nksb92/rlcv3/3d_models/Tube/Stand/floor_stand.FCStd

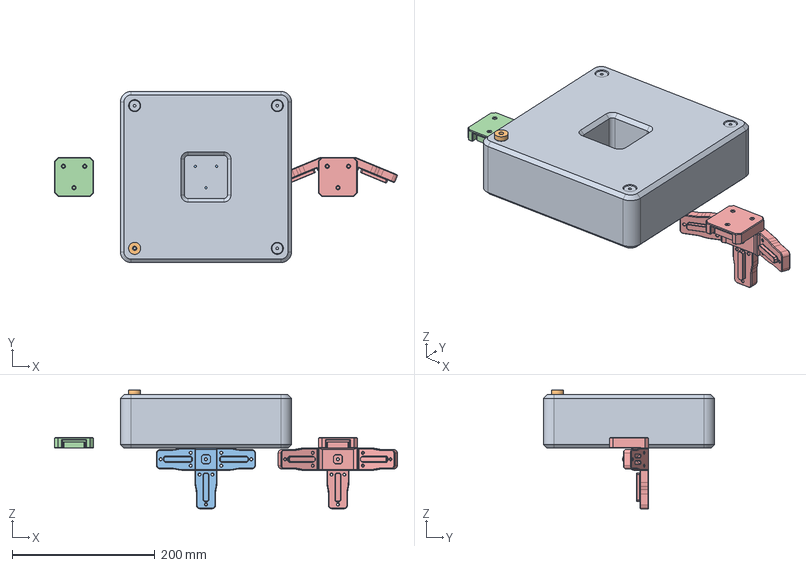
[picture p16: CAD file, 2026-02-27]
3d_models/Tube/Stand/floor_stand.FCStd
480.9 x 240.0 x 166.3 mm
hollow
feet
interface_tube_t_section_clamp
interface_tube_base_clamp
interface_tube_t_section_45°
