nksb92/rlcv3/3d_models/Tube/Connectors/rlcv3_connector_clamp_3.3mf

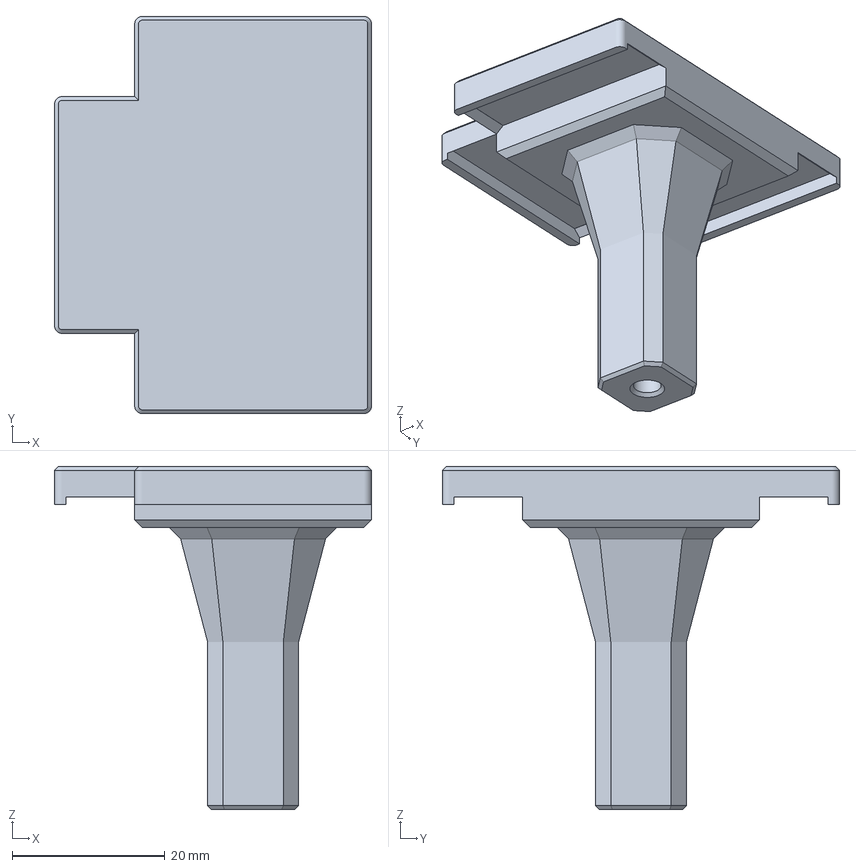
[picture p17: CAD file, 2026-02-27]
3d_models/Tube/Connectors/rlcv3_connector_clamp_3.3mf
41.5 x 52.0 x 44.9 mm
