nksb92/rlcv3/3d_models/Tube/Enclosure/display_spacer.FCStd

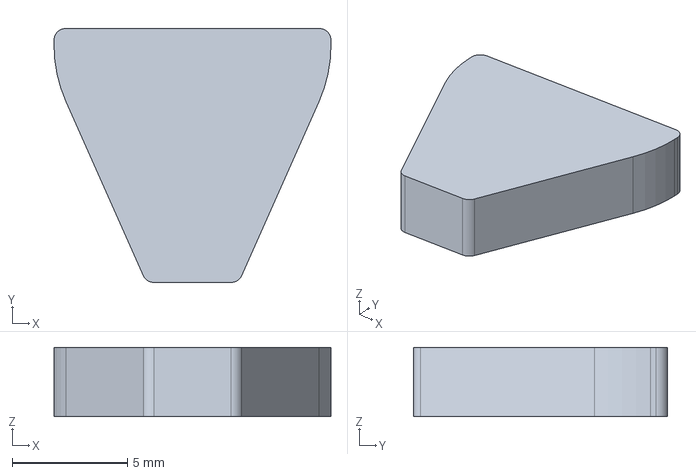
[picture p18: CAD file, 2026-02-27]
3d_models/Tube/Enclosure/display_spacer.FCStd
12.0 x 11.0 x 3.00 mm
