nksb92/rlcv3/3d_models/Tube/Stand/floor_stand_funnel_holder.3mf

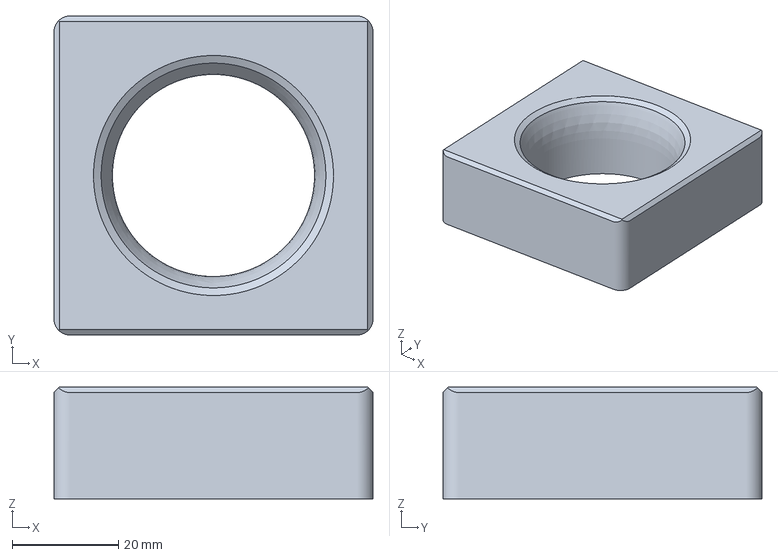
[picture p19: CAD file, 2026-02-27]
3d_models/Tube/Stand/floor_stand_funnel_holder.3mf
60.0 x 60.0 x 21.0 mm
