nksb92/rlcv3/3d_models/Tube/Connectors/rlcv3_connector_90_degree.3mf

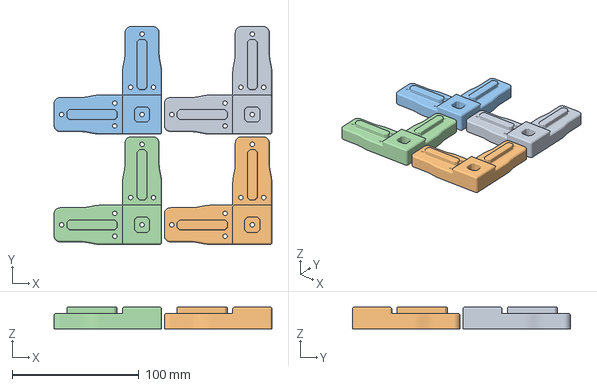
[picture p20: CAD file, 2026-02-27]
3d_models/Tube/Connectors/rlcv3_connector_90_degree.3mf
172.0 x 172.0 x 17.0 mm
