nksb92/rlcv3/3d_models/Tube/Enclosure/rlcv3_bottom.stp

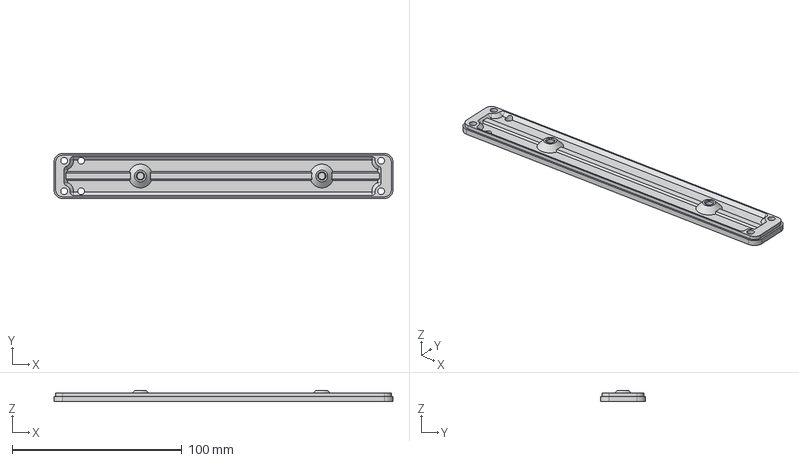
[picture p21: CAD file, 2026-02-27]
3d_models/Tube/Enclosure/rlcv3_bottom.stp
200.0 x 26.5 x 6.50 mm
