nksb92/rlcv3/3d_models/Tube/Stand/floor_stand_funnel.3mf

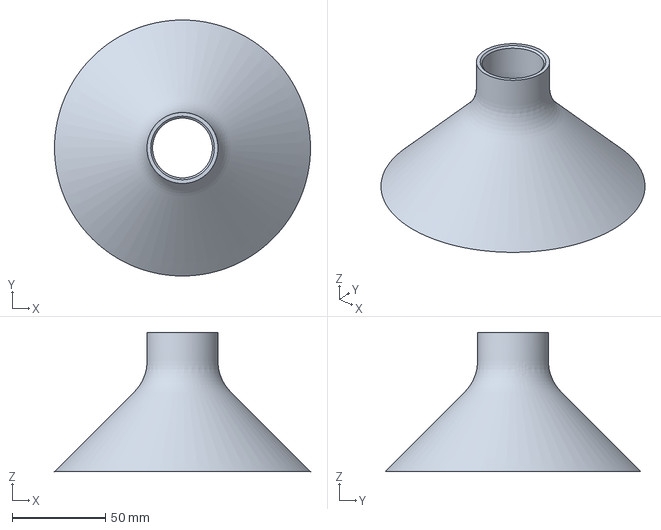
[picture p22: CAD file, 2026-02-27]
3d_models/Tube/Stand/floor_stand_funnel.3mf
137.0 x 137.0 x 74.5 mm
