nksb92/rlcv3/3d_models/Tube/Connectors/rlcv3_connector_t_section_45°.3mf

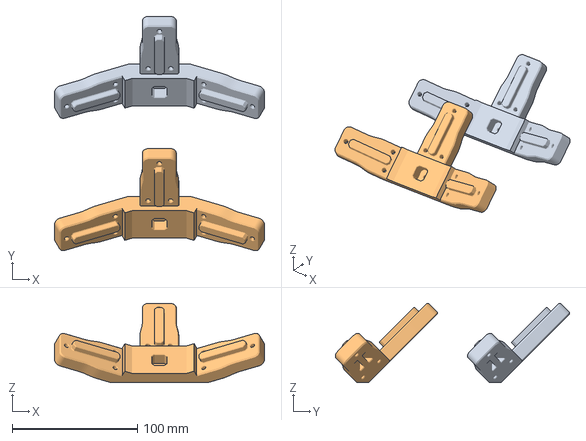
[picture p23: CAD file, 2026-02-27]
3d_models/Tube/Connectors/rlcv3_connector_t_section_45°.3mf
167.4 x 186.8 x 63.2 mm
