nksb92/rlcv3/3d_models/Tube/Enclosure/rlcv3_top.stp

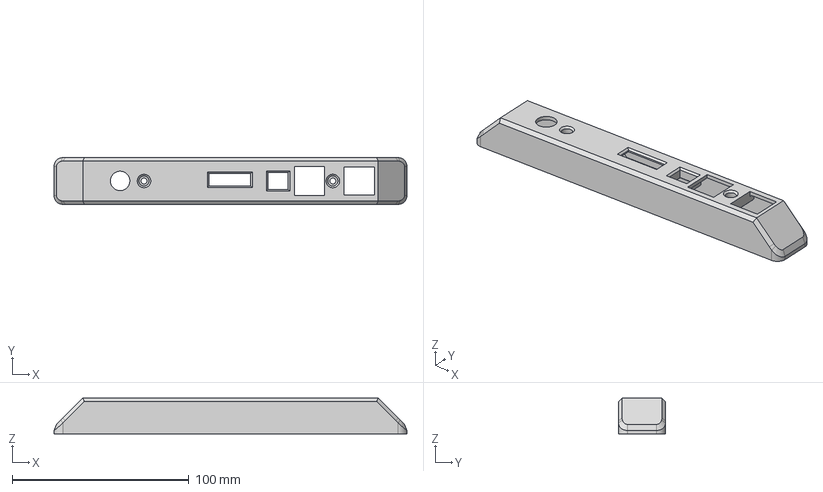
[picture p24: CAD file, 2026-02-27]
3d_models/Tube/Enclosure/rlcv3_top.stp
200.0 x 26.5 x 20.4 mm
