nksb92/rlcv3/3d_models/Tube/Connectors/rlcv3_connector_t_section.3mf

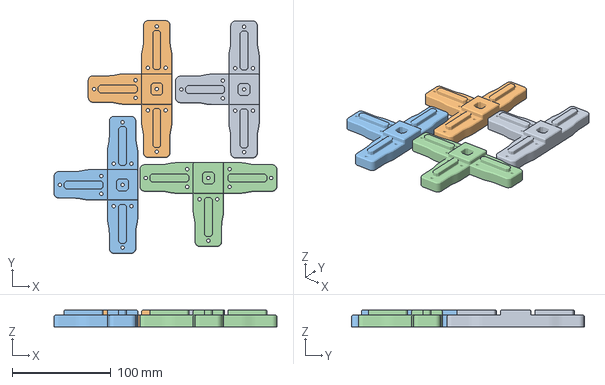
[picture p25: CAD file, 2026-02-27]
3d_models/Tube/Connectors/rlcv3_connector_t_section.3mf
226.0 x 236.1 x 17.0 mm
