nksb92/rlcv3/3d_models/Tube/Connectors/rlcv3_connector_adapter_spots_connector.3mf

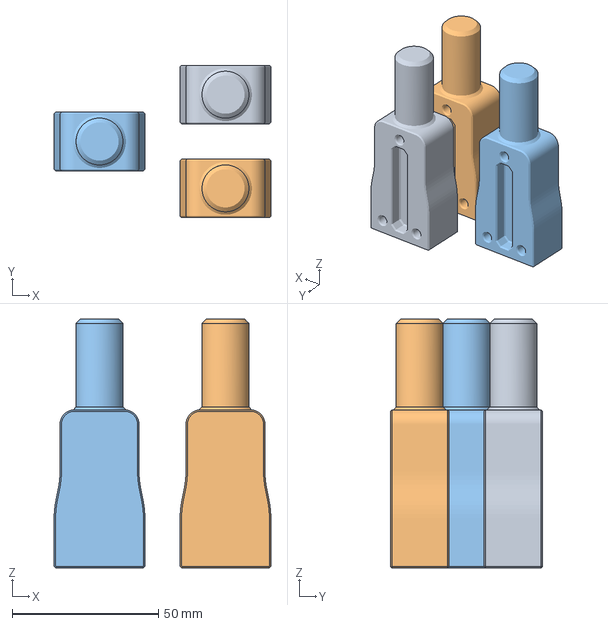
[picture p26: CAD file, 2026-02-27]
3d_models/Tube/Connectors/rlcv3_connector_adapter_spots_connector.3mf
74.0 x 52.0 x 85.0 mm
