nksb92/rlcv3/RLC_V3/nvm.cpp

#include "nvm.h"

#define COUNT_STORED_VALUES 14
#define POLYNOMIAL 0xD8
#define WIDTH (8 * sizeof(uint8_t))
#define TOPBIT (1 << (WIDTH - 1))
#define REFLECT_DATA(X) ((uint8_t)reflect((X), 8))
#define REFLECT_REMAINDER(X) ((uint8_t)reflect((X), WIDTH))
uint8_t crcTable[256];

// crc code from website: https://barrgroup.com/embedded-systems/how-to/crc-calculation-c-code
// explaination can be found there
void crcInit() {
  uint8_t remainder;

  for (int dividend = 0; dividend < 256; ++dividend) {
    remainder = dividend << (WIDTH - 8);

    for (uint8_t bit = 8; bit > 0; --bit) {
      if (remainder & TOPBIT) {
        remainder = (remainder << 1) ^ POLYNOMIAL;
      } else {
        remainder = (remainder << 1);
      }
    }
    crcTable[dividend] = remainder;
  }
}

uint8_t crcFast(int message[]) {
  uint8_t data;
  uint8_t remainder = 0;
  int nBytes = sizeof(message);

  for (int byte = 0; byte < nBytes; ++byte) {
    data = message[byte] ^ (remainder >> (WIDTH - 8));
    remainder = crcTable[data] ^ (remainder << 8);
  }

  return (remainder);
}

void init_eeprom() {
  EEPROM.begin(EEPROM_ADDRESSES);
  crcInit();
}

void read_eeprom(C_HSV& hsv_val, C_RGB& rgb_val, rgb_dmx& dmx_val, menu_structure& main_sw, rlc_artnet& artnet_var, segments& segment_var) {
  uint16_t eeprom_address = 0;
  int crc_values[COUNT_STORED_VALUES] = {};
  uint8_t crc_index = 0;

  // get all variables from the hsv page
  uint8_t hue = STD_HUE;
  EEPROM.get(eeprom_address, hue);
  eeprom_address += sizeof(hue);
  crc_values[crc_index] = hue;
  crc_index++;

  uint8_t sat = STD_SAT;
  EEPROM.get(eeprom_address, sat);
  eeprom_address += sizeof(sat);
  crc_values[crc_index] = sat;
  crc_index++;

  uint8_t val = STD_VAL;
  EEPROM.get(eeprom_address, val);
  eeprom_address += sizeof(sat);
  crc_values[crc_index] = val;
  crc_index++;

  // get all variables from the rgb page
  uint8_t red = STD_RED;
  EEPROM.get(eeprom_address, red);
  eeprom_address += sizeof(red);
  crc_values[crc_index] = red;
  crc_index++;

  uint8_t green = STD_GREEN;
  EEPROM.get(eeprom_address, green);
  eeprom_address += sizeof(green);
  crc_values[crc_index] = green;
  crc_index++;

  uint8_t blue = STD_BLUE;
  EEPROM.get(eeprom_address, blue);
  eeprom_address += sizeof(blue);
  crc_values[crc_index] = blue;
  crc_index++;

  // get all variables from the segment page
  uint8_t segment_pos = STD_SEGMENTS;
  EEPROM.get(eeprom_address, segment_pos);
  eeprom_address += sizeof(segment_pos);
  crc_values[crc_index] = segment_pos;
  crc_index++;

  // get all variables from the dmx page
  uint16_t start_address = STD_START_ADDRESS;
  EEPROM.get(eeprom_address, start_address);
  eeprom_address += sizeof(start_address);
  crc_values[crc_index] = start_address;
  crc_index++;

  // get the current main state
  uint8_t current_main = STD_CURRENT;
  EEPROM.get(eeprom_address, current_main);
  eeprom_address += sizeof(current_main);
  crc_values[crc_index] = current_main;
  crc_index++;

  uint8_t deepness_main = STD_DEEPNESS;
  EEPROM.get(eeprom_address, deepness_main);
  eeprom_address += sizeof(deepness_main);
  crc_values[crc_index] = deepness_main;
  crc_index++;

  // get all variables from the artnet page
  uint16_t artnet_universe = STD_UNIVERSE;
  EEPROM.get(eeprom_address, artnet_universe);
  eeprom_address += sizeof(artnet_universe);
  crc_values[crc_index] = artnet_universe;
  crc_index++;

  uint16_t artnet_start = STD_START_ADDRESS;
  EEPROM.get(eeprom_address, artnet_start);
  eeprom_address += sizeof(artnet_start);
  crc_values[crc_index] = artnet_start;
  crc_index++;

  uint8_t artnet_fsm = MENU;
  EEPROM.get(eeprom_address, artnet_fsm);
  eeprom_address += sizeof(artnet_fsm);
  crc_values[crc_index] = artnet_fsm;

  uint8_t crc = 0;
  EEPROM.get(eeprom_address, crc);

  // checking if the saved crc matches the calculated
  // and sets the corresponding variables on success
  if (crc == crcFast(crc_values)) {
    hsv_val.set_hue_byte(hue);
    hsv_val.set_sat(sat);
    hsv_val.set_val(val);

    rgb_val.set_red(red);
    rgb_val.set_green(green);
    rgb_val.set_blue(blue);

    segment_var.set_current_segment(segment_pos);

    dmx_val.set_number_segments(segment_var.get_num_seg());
    artnet_var.set_number_segments(segment_var.get_num_seg());

    dmx_val.set_start_address(start_address);

    main_sw.set_current(current_main);
    main_sw.set_deepness(deepness_main);

    artnet_var.set_current_universe_nmbr(artnet_universe);
    artnet_var.set_current_channel(artnet_start);
    artnet_var.set_current_fsm(artnet_fsm);
  }
}

void write_eeprom(C_HSV& hsv_val, C_RGB& rgb_val, rgb_dmx& dmx_val, menu_structure& main_sw, rlc_artnet& artnet_var, segments& segment_var) {
  uint16_t eeprom_address = 0;
  int crc_values[COUNT_STORED_VALUES] = {};
  uint8_t crc_index = 0;

  // set all variables from the hsv page
  uint8_t hue = hsv_val.get_hue();
  EEPROM.put(eeprom_address, hue);
  eeprom_address += sizeof(hue);
  crc_values[crc_index] = hue;
  crc_index++;

  uint8_t sat = hsv_val.get_sat();
  EEPROM.put(eeprom_address, sat);
  eeprom_address += sizeof(sat);
  crc_values[crc_index] = sat;
  crc_index++;

  uint8_t val = hsv_val.get_val();
  EEPROM.put(eeprom_address, val);
  eeprom_address += sizeof(val);
  crc_values[crc_index] = val;
  crc_index++;

  // set all variables from the rgb page
  uint8_t red = rgb_val.get_red();
  EEPROM.put(eeprom_address, red);
  eeprom_address += sizeof(red);
  crc_values[crc_index] = red;
  crc_index++;

  uint8_t green = rgb_val.get_green();
  EEPROM.put(eeprom_address, green);
  eeprom_address += sizeof(green);
  crc_values[crc_index] = green;
  crc_index++;

  uint8_t blue = rgb_val.get_blue();
  EEPROM.put(eeprom_address, blue);
  eeprom_address += sizeof(blue);
  crc_values[crc_index] = blue;
  crc_index++;

  // set all variables from the segment page
  uint8_t segment_pos = segment_var.get_current_seg();
  EEPROM.put(eeprom_address, segment_pos);
  eeprom_address += sizeof(segment_pos);
  crc_values[crc_index] = segment_pos;
  crc_index++;

  // set all variables from the dmx page
  uint16_t start_address = dmx_val.get_start();
  EEPROM.put(eeprom_address, start_address);
  eeprom_address += sizeof(start_address);
  crc_values[crc_index] = start_address;
  crc_index++;

  // set the all variables from main state
  uint8_t current_main = main_sw.get_current();
  EEPROM.put(eeprom_address, current_main);
  eeprom_address += sizeof(current_main);
  crc_values[crc_index] = current_main;
  crc_index++;

  uint8_t deepness_main = main_sw.get_deepness();
  EEPROM.put(eeprom_address, deepness_main);
  eeprom_address += sizeof(deepness_main);
  crc_values[crc_index] = deepness_main;
  crc_index++;

  // set all variables from the artnet page
  uint16_t artnet_universe = artnet_var.get_start_universe();
  EEPROM.put(eeprom_address, artnet_universe);
  eeprom_address += sizeof(artnet_universe);
  crc_values[crc_index] = artnet_universe;
  crc_index++;

  uint16_t artnet_start = artnet_var.get_start_channel();
  EEPROM.put(eeprom_address, artnet_start);
  eeprom_address += sizeof(artnet_start);
  crc_values[crc_index] = artnet_start;
  crc_index++;

  uint8_t artnet_fsm = artnet_var.get_current_fsm();
  EEPROM.put(eeprom_address, artnet_fsm);
  eeprom_address += sizeof(artnet_fsm);
  crc_values[crc_index] = artnet_fsm;

  // calculate the crc and saving it in the eeprom
  EEPROM.put(eeprom_address, crcFast(crc_values));

  EEPROM.commit();
}
