nksb92/rlcv3/RLC_V3/common.h

#ifndef COMMON_H
#define COMMON_H

#include <Arduino.h>
#include <FastLED.h>

#include "c_hsv.h"
#include "c_rgb.h"
#include "config.h"
#include "menu_structure.h"
#include "rlc_artnet.h"
#include "settings_menu.h"
#include "std_defines.h"

#endif
