nksb92/rlcv3/RLC_V3/src/common.h

#ifndef COMMON_H
#define COMMON_H

#include <Arduino.h>
#include <FastLED.h>
#include "rlc_artnet.h"
#include "std_defines.h"
#include "config.h"

#include <menu_structure.h>
#include <c_hsv.h>
#include <c_rgb.h>

#endif
